robzach/ISAM_102_workshop/production files/knobs/knob_h25_t30_c1.stl

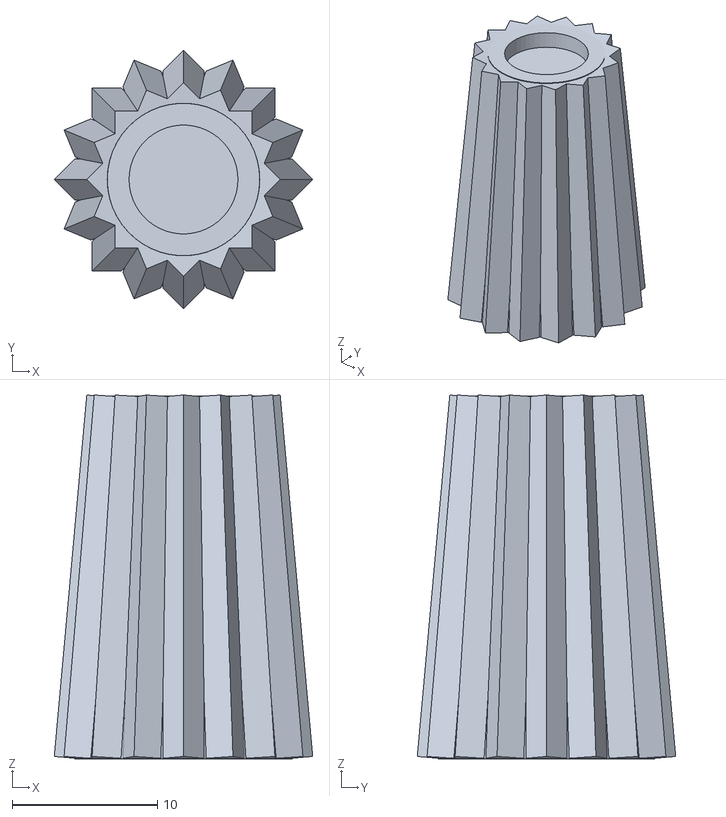
[picture p17: CAD file, 2025-09-17]
production files/knobs/knob_h25_t30_c1.stl
17.8 x 17.8 x 25.1
