robzach/ISAM_102_workshop/production files/L2_Support_Arch.dxf

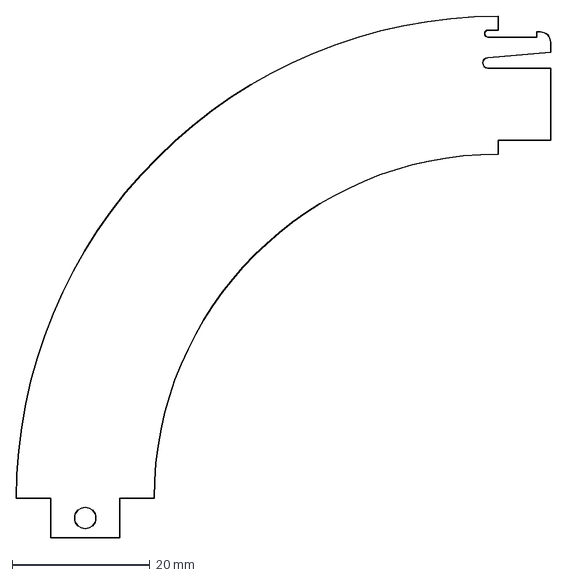
[picture p19: CAD file, 2024-09-11]
production files/L2_Support_Arch.dxf
77.6 x 75.7 mm
