robzach/ISAM_102_workshop/production files/L13_Sidewall.dxf

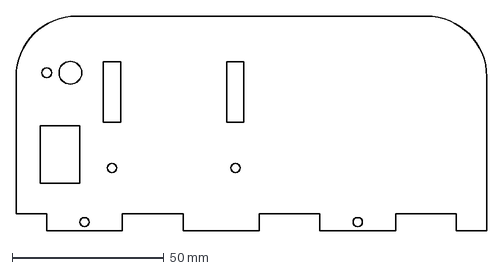
[picture p21: CAD file, 2024-09-11]
production files/L13_Sidewall.dxf
155.0 x 70.7 mm
