robzach/ISAM_102_workshop/production files/knobs/knob_h20_t40_c2.stl

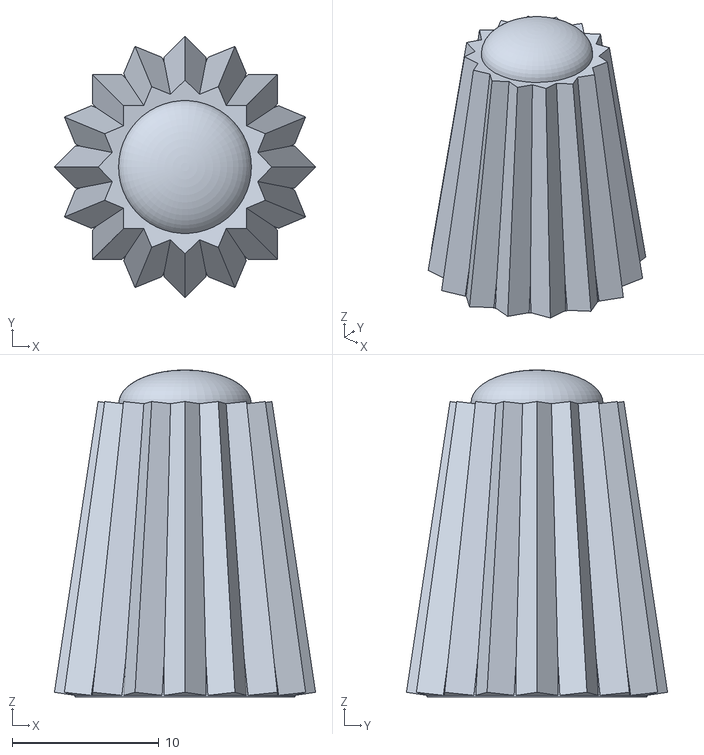
[picture p22: CAD file, 2025-09-17]
production files/knobs/knob_h20_t40_c2.stl
17.8 x 17.8 x 22.2
