robzach/ISAM_102_workshop/production files/L8_Dog_Head.dxf

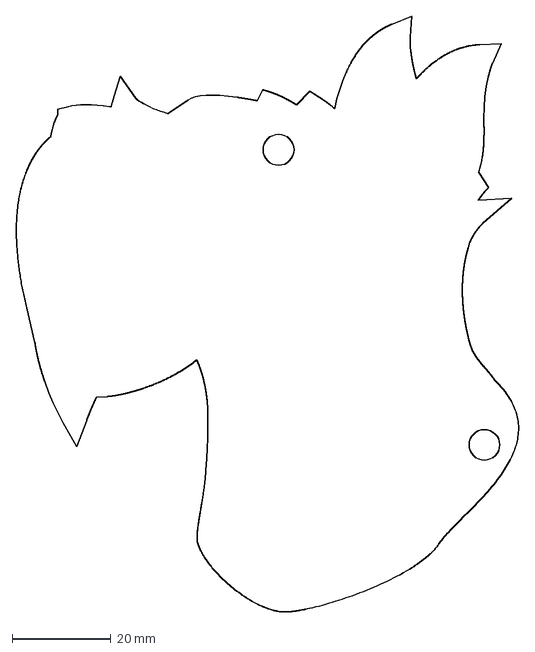
[picture p23: CAD file, 2024-09-11]
production files/L8_Dog_Head.dxf
101.5 x 120.4 mm
