robzach/ISAM_102_workshop/production files/knobs/knob_h15_t0_c2.stl

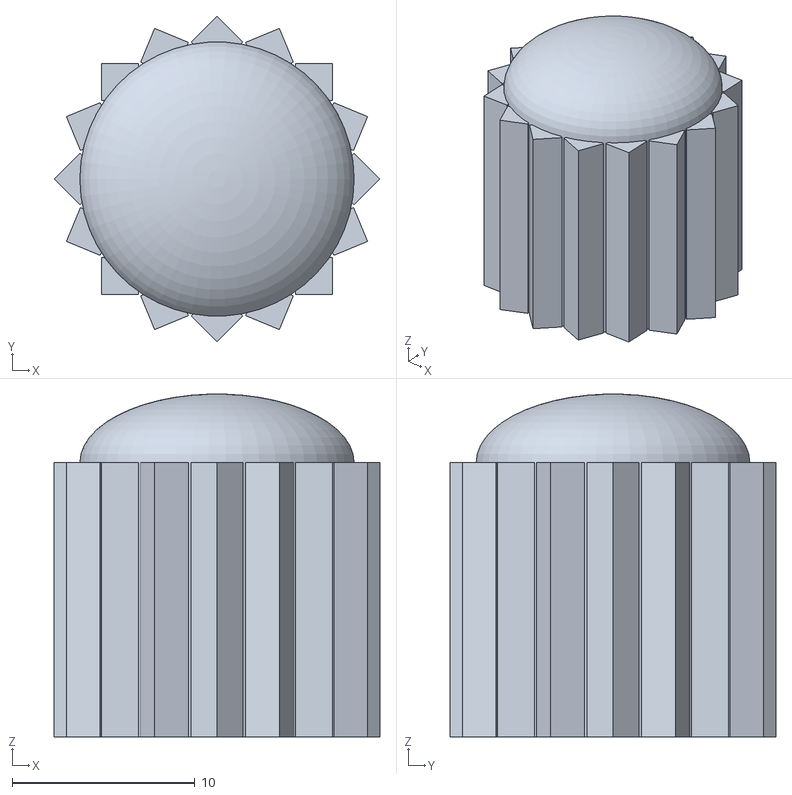
[picture p25: CAD file, 2025-09-17]
production files/knobs/knob_h15_t0_c2.stl
17.8 x 17.8 x 18.7
