robzach/ISAM_102_workshop/production files/L12_SquareCam.dxf

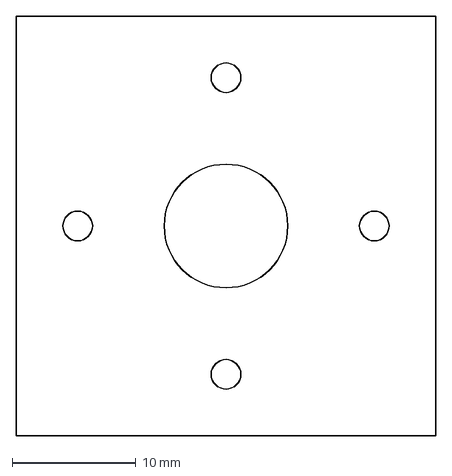
[picture p26: CAD file, 2024-09-11]
production files/L12_SquareCam.dxf
33.9 x 33.9 mm
