robzach/ISAM_102_workshop/production files/L14_SpiralCam.dxf

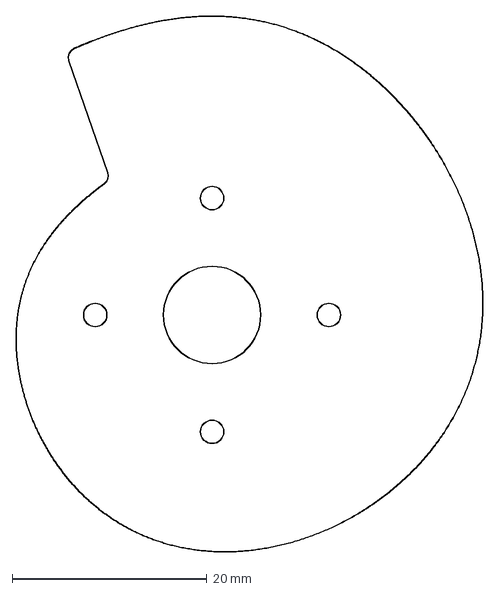
[picture p28: CAD file, 2024-09-11]
production files/L14_SpiralCam.dxf
47.9 x 55.0 mm
