robzach/ISAM_102_workshop/production files/L5_L6_Gears.dxf

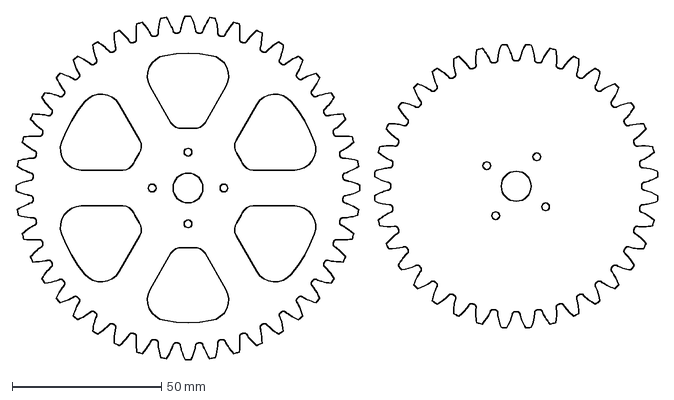
[picture p30: CAD file, 2024-09-11]
production files/L5_L6_Gears.dxf
214.7 x 115.0 mm
