robzach/ISAM_102_workshop/production files/knobs/knob_h25_t0_c2.stl

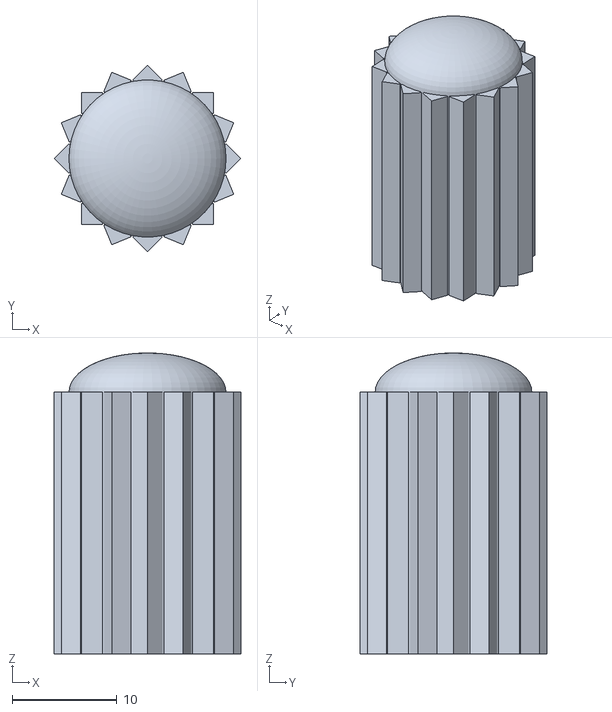
[picture p31: CAD file, 2025-09-17]
production files/knobs/knob_h25_t0_c2.stl
17.8 x 17.8 x 28.7
