robzach/ISAM_102_workshop/production files/L9_PentaCam.dxf

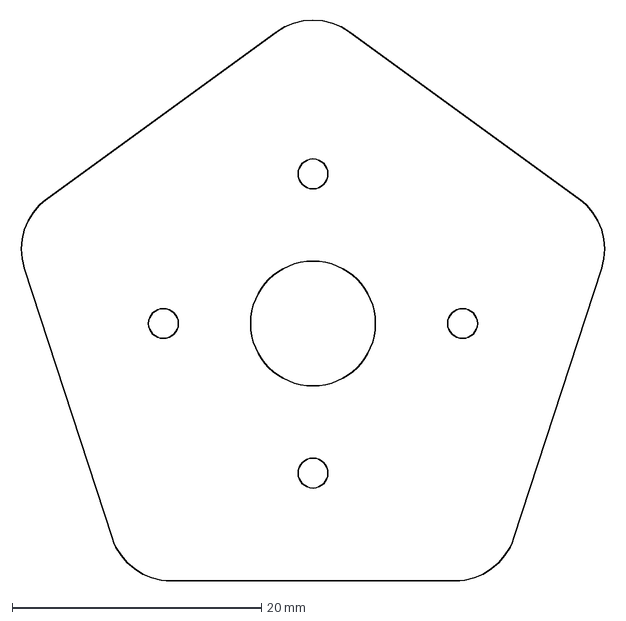
[picture p32: CAD file, 2024-09-11]
production files/L9_PentaCam.dxf
47.6 x 45.3 mm
