robzach/ISAM_102_workshop/production files/L10_Pointy_Cam.dxf

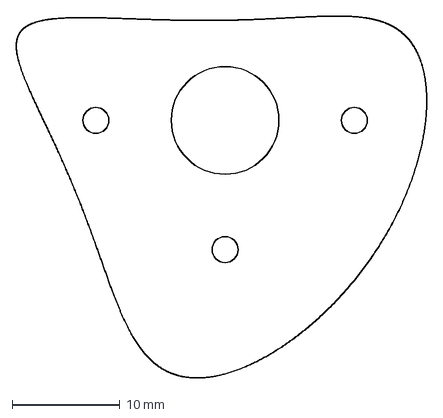
[picture p34: CAD file, 2024-09-11]
production files/L10_Pointy_Cam.dxf
38.1 x 33.6 mm
