robzach/ISAM_102_workshop/production files/knobs/knob_h20_t40_c1.stl

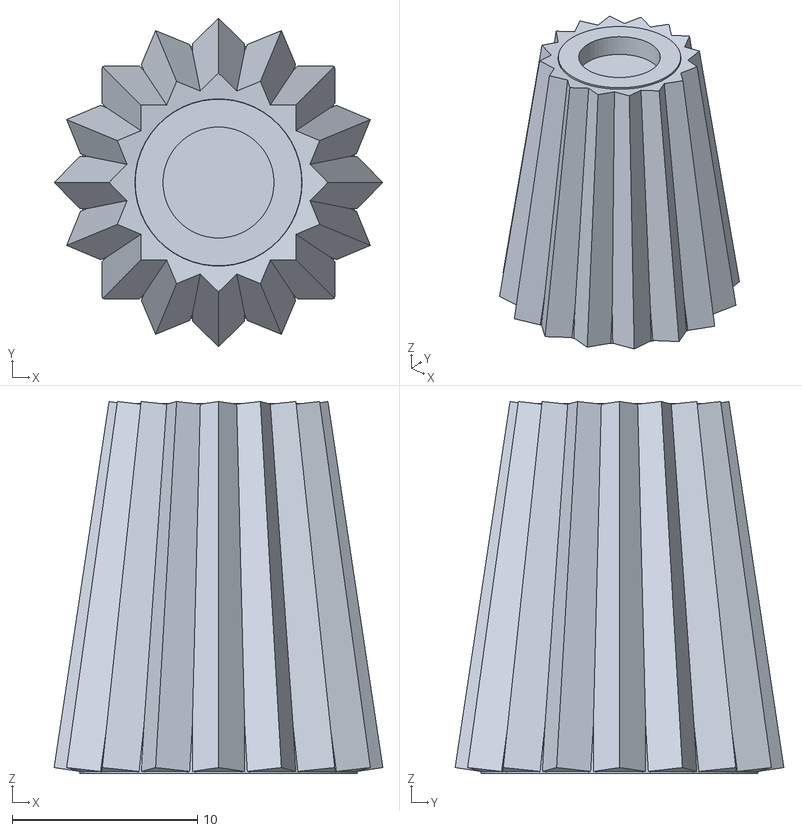
[picture p35: CAD file, 2025-09-17]
production files/knobs/knob_h20_t40_c1.stl
17.8 x 17.8 x 20.1
