robzach/ISAM_102_workshop/production files/L7_Dog_Body.dxf

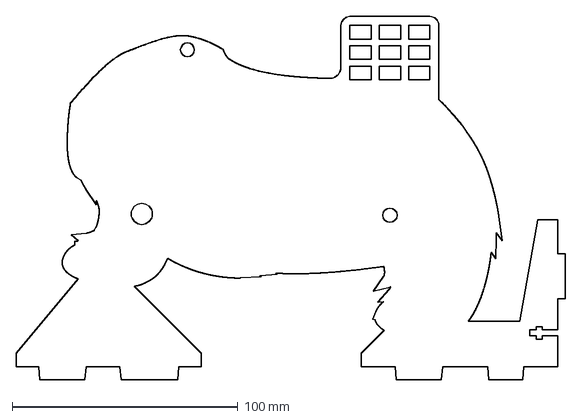
[picture p36: CAD file, 2024-09-11]
production files/L7_Dog_Body.dxf
243.0 x 160.7 mm
