robzach/ISAM_102_workshop/production files/L3_Base.dxf

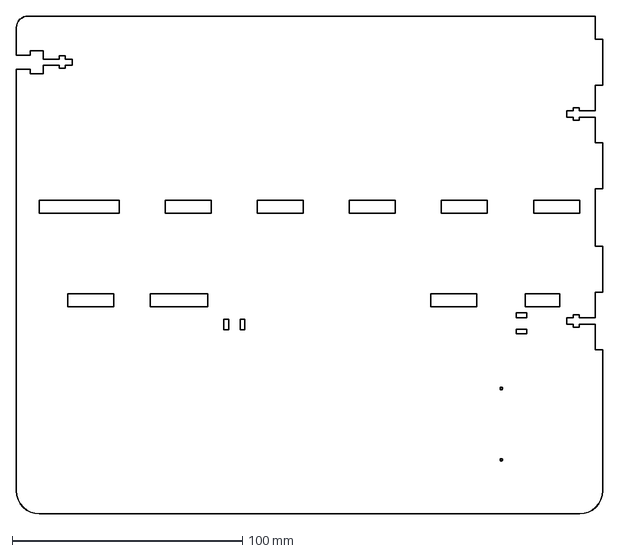
[picture p38: CAD file, 2024-09-11]
production files/L3_Base.dxf
254.7 x 216.3 mm
