robzach/ISAM_102_workshop/production files/L11_RoundCam.dxf

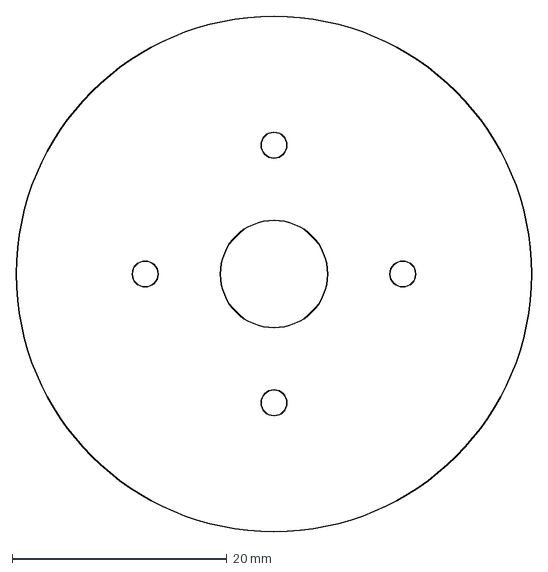
[picture p40: CAD file, 2024-09-11]
production files/L11_RoundCam.dxf
48.0 x 48.0 mm
