robzach/ISAM_102_workshop/production files/knobs/knob_h25_t30_c2.stl

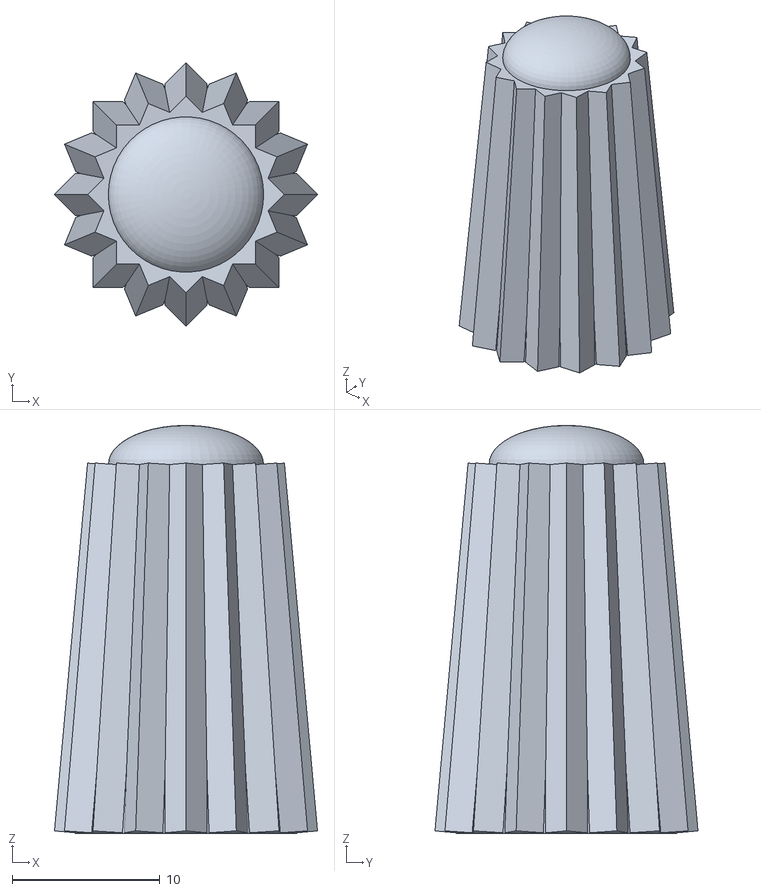
[picture p41: CAD file, 2025-09-17]
production files/knobs/knob_h25_t30_c2.stl
17.8 x 17.8 x 27.6
