robzach/ISAM_102_workshop/production files/L1_Acrylic_Wall.dxf

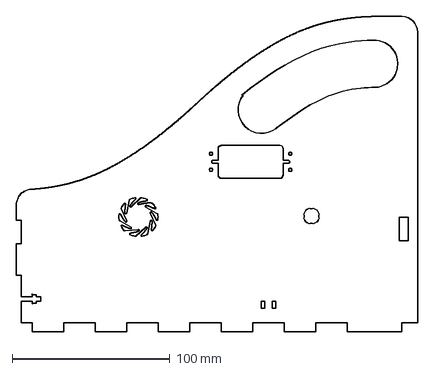
[picture p42: CAD file, 2024-09-11]
production files/L1_Acrylic_Wall.dxf
254.7 x 200.0 mm
