robzach/ISAM_102_workshop/production files/L4_Gear_12Tooth.dxf

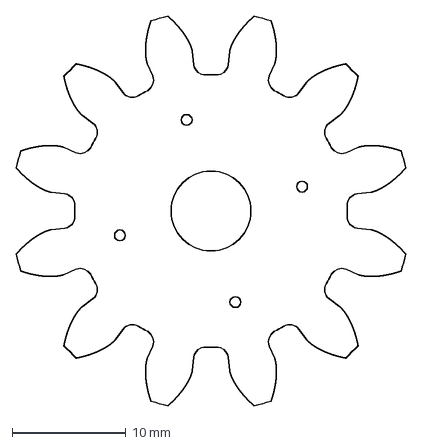
[picture p44: CAD file, 2024-09-11]
production files/L4_Gear_12Tooth.dxf
34.2 x 34.2 mm
