robzach/ISAM_102_workshop/production files/parameterized hub design v5.stl

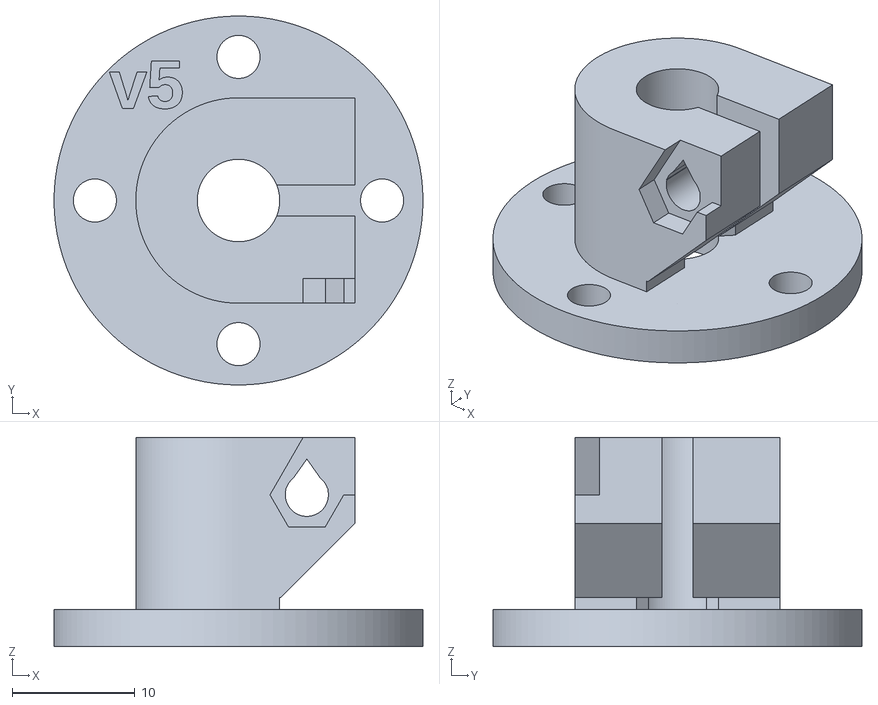
[picture p46: CAD file, 2024-09-11]
production files/parameterized hub design v5.stl
30.0 x 30.0 x 17.0
