robzach/ISAM_102_workshop/production files/knobs/knob_h20_t50_c2.stl

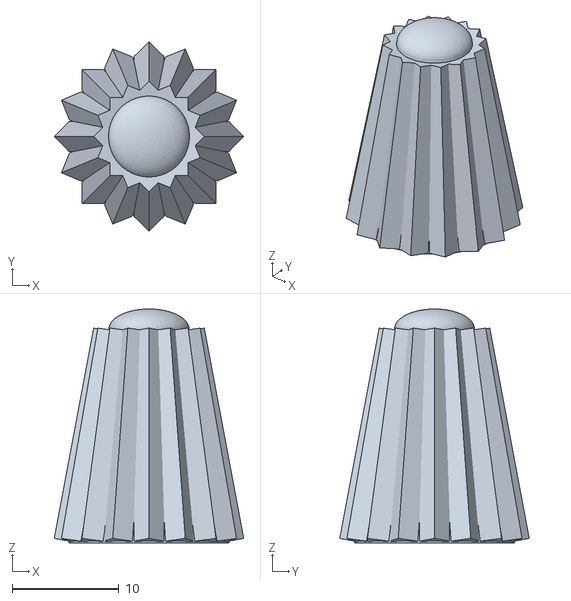
[picture p51: CAD file, 2025-09-17]
production files/knobs/knob_h20_t50_c2.stl
17.7 x 17.7 x 21.9
