robzach/ISAM_102_workshop/production files/knobs/knob_h30_t30_c2.stl

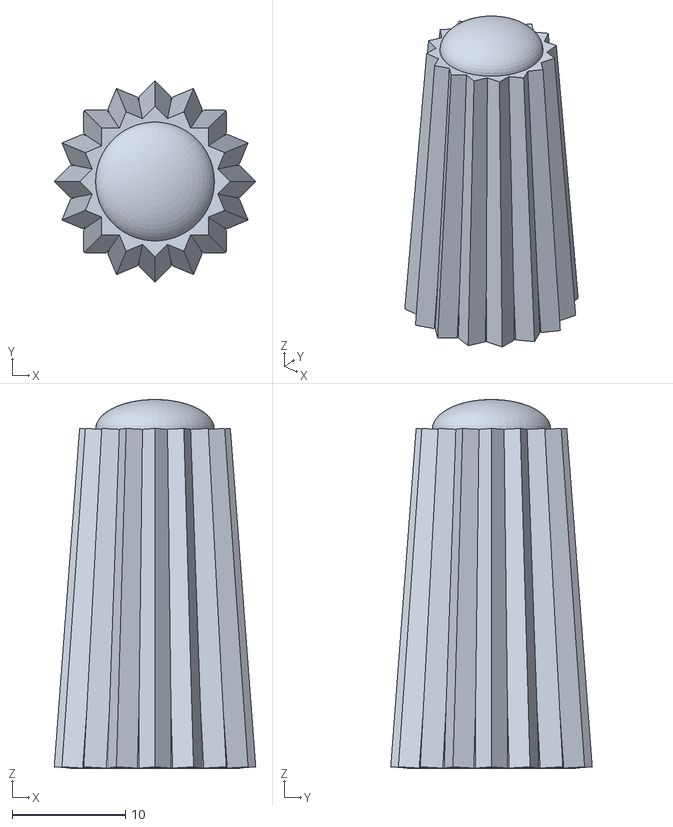
[picture p52: CAD file, 2025-09-17]
production files/knobs/knob_h30_t30_c2.stl
17.8 x 17.8 x 32.6
