robzach/ISAM_102_workshop/production files/knobs/knob_h20_t10_c1.stl

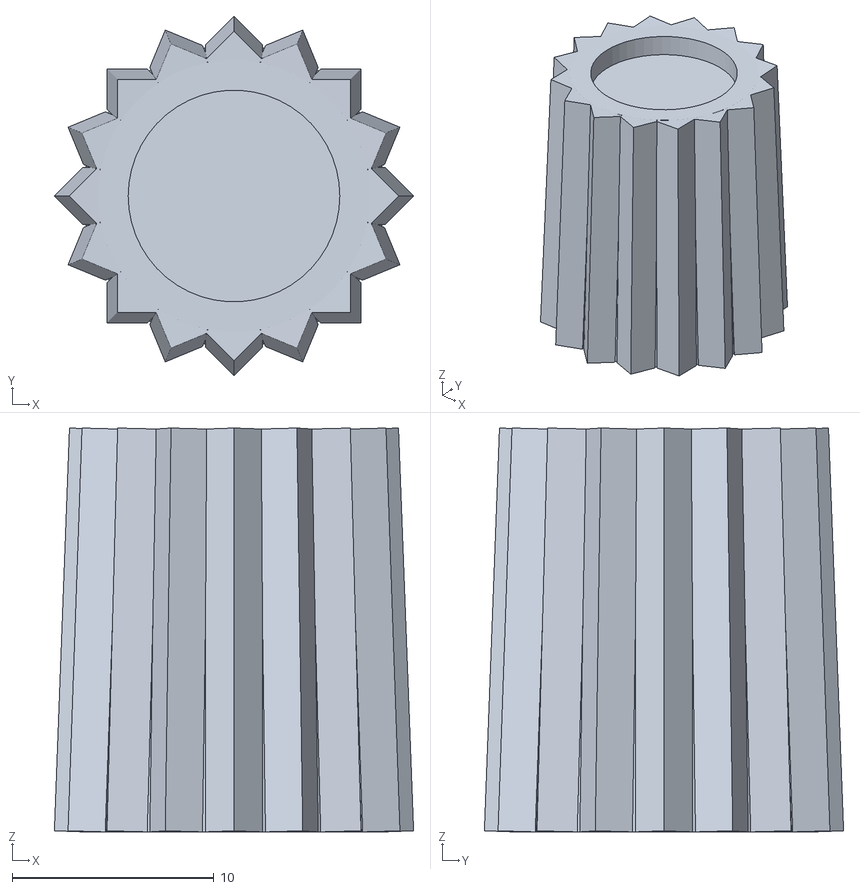
[picture p53: CAD file, 2025-09-17]
production files/knobs/knob_h20_t10_c1.stl
17.8 x 17.8 x 20.0
