robzach/ISAM_102_workshop/production files/knobs/knob_h15_t50_c1.stl

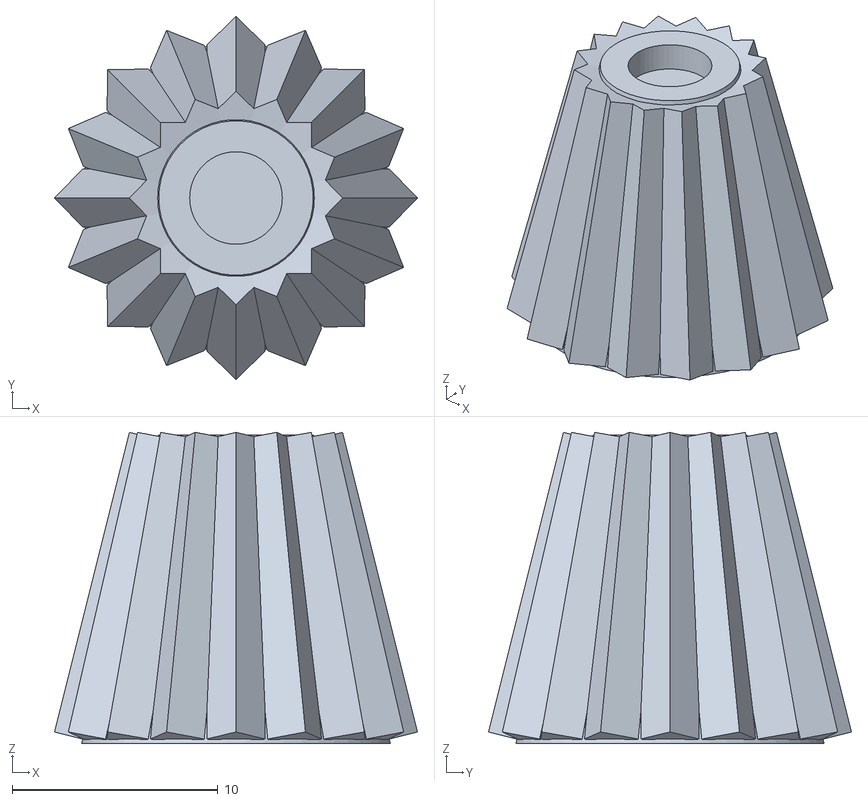
[picture p63: CAD file, 2025-09-17]
production files/knobs/knob_h15_t50_c1.stl
17.6 x 17.6 x 15.1
