robzach/ISAM_102_workshop/production files/knobs/knob_h30_t10_c2.stl

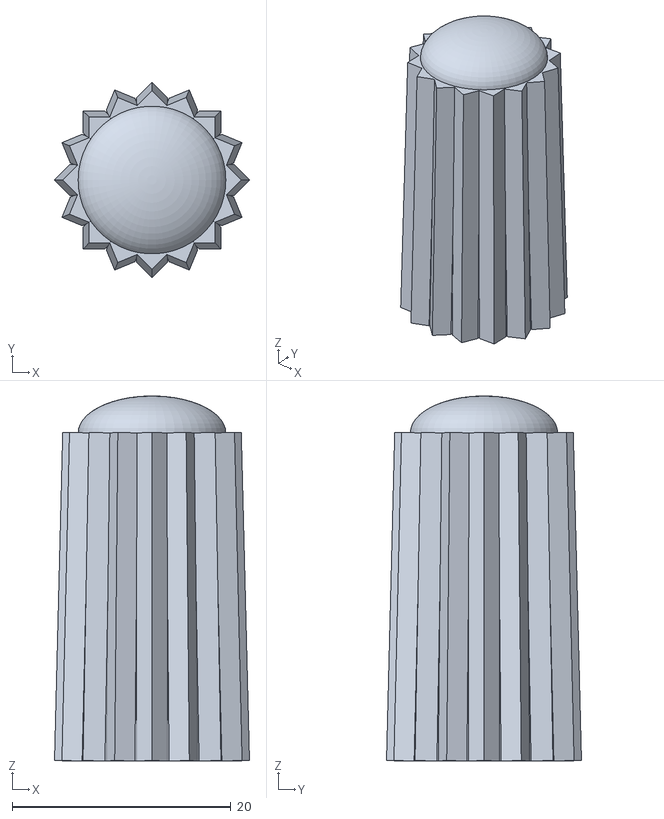
[picture p68: CAD file, 2025-09-17]
production files/knobs/knob_h30_t10_c2.stl
17.8 x 17.8 x 33.4
